Donatussss/Final_year_project_undergrad/Firmware/oxygen_harvester/Core/Inc/water.h

#ifndef INC_WATER_H_
#define INC_WATER_H_

void waterInitialization();
void waterManagement();
void waterLevel_Chamber_1(int chamberMin, int chamberMax);
void waterLevel_Chamber_2(int chamberMin, int chamberMax);
void waterLevel_Chamber_3(int chamberMin, int chamberMax);
void waterLevel_Chamber_4(int chamberMin, int chamberMax);

#endif /* INC_WATER_H_ */
